uwmadisonieee/Bluetooth-Retro-DJ/3D_Models/LED_Speaker/1-8inch_TFT_Color_LCD.png

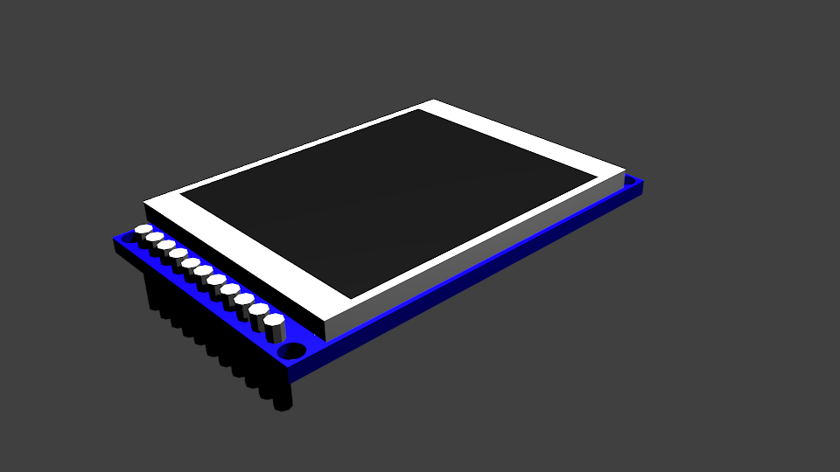
3D_Models/LED_Speaker/1-8inch_TFT_Color_LCD.png
