uwmadisonieee/Bluetooth-Retro-DJ/3D_Models/LED_Speaker/LED_Spin_Speaker_V1_Render.gif

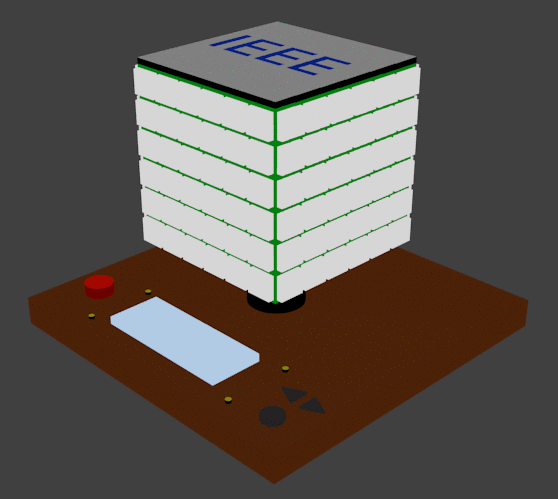
3D_Models/LED_Speaker/LED_Spin_Speaker_V1_Render.gif
