uwmadisonieee/Bluetooth-Retro-DJ/code/LED_Speaker/display/gifs/0.gif

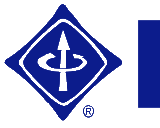
code/LED_Speaker/display/gifs/0.gif
