uwmadisonieee/Bluetooth-Retro-DJ/code/LED_Speaker/display/gifs/1.gif

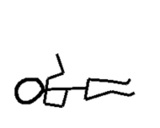
code/LED_Speaker/display/gifs/1.gif
