uwmadisonieee/Bluetooth-Retro-DJ/code/LED_Speaker/display/gifs/2.gif

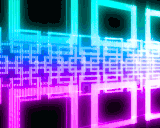
code/LED_Speaker/display/gifs/2.gif
