uwmadisonieee/Bluetooth-Retro-DJ/code/LED_Speaker/display/gifs/3.gif

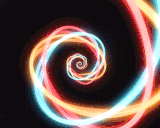
code/LED_Speaker/display/gifs/3.gif
