uwmadisonieee/Bluetooth-Retro-DJ/code/LED_Speaker/display/gifs/4.gif

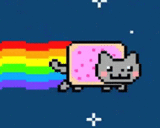
code/LED_Speaker/display/gifs/4.gif
