uwmadisonieee/Bluetooth-Retro-DJ/code/LED_Speaker/display/gifs/5.gif

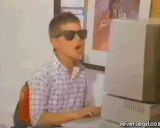
code/LED_Speaker/display/gifs/5.gif
