uwmadisonieee/Bluetooth-Retro-DJ/code/LED_Speaker/display/gifs/6.gif

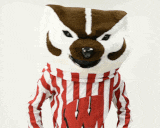
code/LED_Speaker/display/gifs/6.gif
