uwmadisonieee/Bluetooth-Retro-DJ/code/LED_Speaker/display/gifs/7.gif

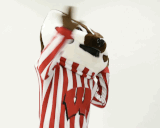
code/LED_Speaker/display/gifs/7.gif
