uwmadisonieee/Bluetooth-Retro-DJ/code/LED_Speaker/display/gifs/8.gif

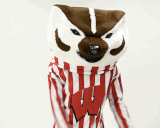
code/LED_Speaker/display/gifs/8.gif
