uwmadisonieee/Bluetooth-Retro-DJ/code/LED_Speaker/display/gifs/9.gif

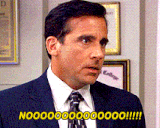
code/LED_Speaker/display/gifs/9.gif
