uwmadisonieee/Bluetooth-Retro-DJ/code/LED_Speaker/display/gifs/10.gif

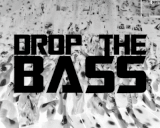
code/LED_Speaker/display/gifs/10.gif
