uwmadisonieee/Bluetooth-Retro-DJ/code/LED_Speaker/display/gifs/11.gif

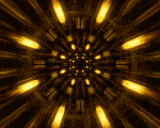
code/LED_Speaker/display/gifs/11.gif
